Bagnis-Gabriele/Robotic-hand/photos/hands/High_five.jpg

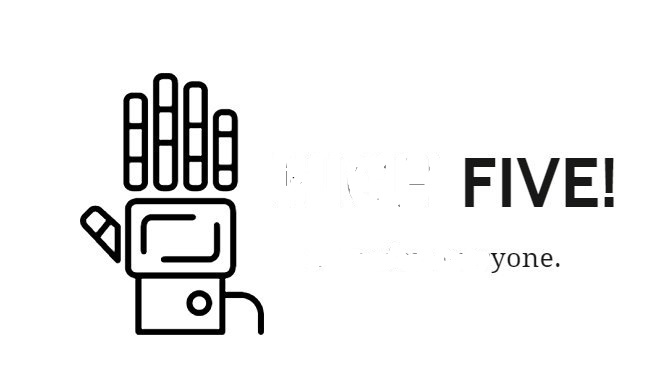
photos/hands/High_five.jpg
