Bagnis-Gabriele/Robotic-hand/photos/hands/mano_complited.jpg

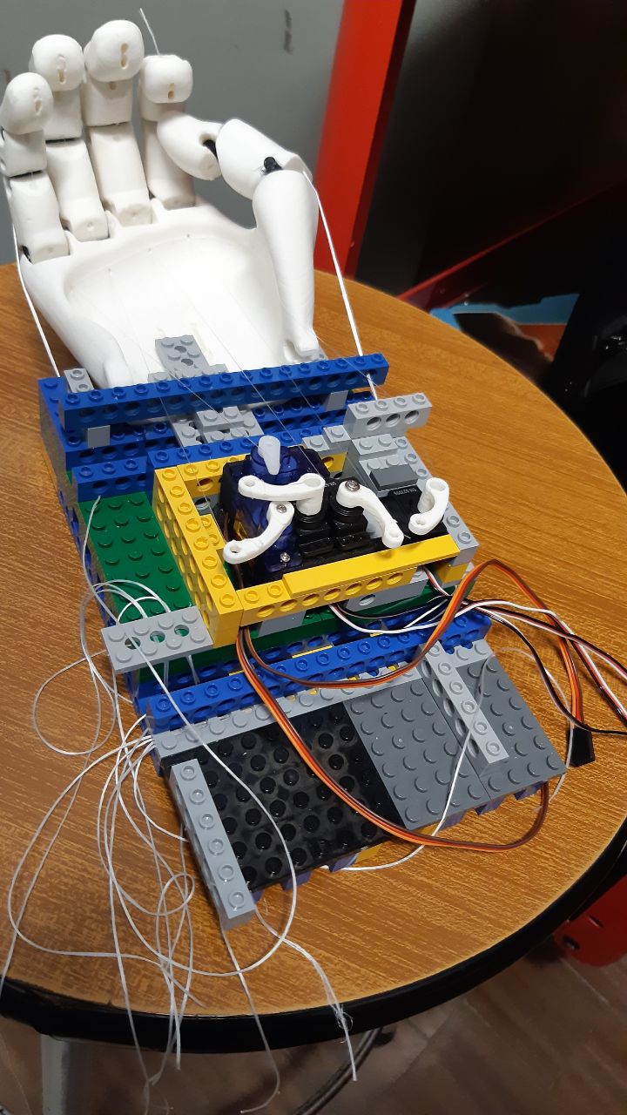
photos/hands/mano_complited.jpg
