Bagnis-Gabriele/Robotic-hand/photos/Insta/emotive.jpg

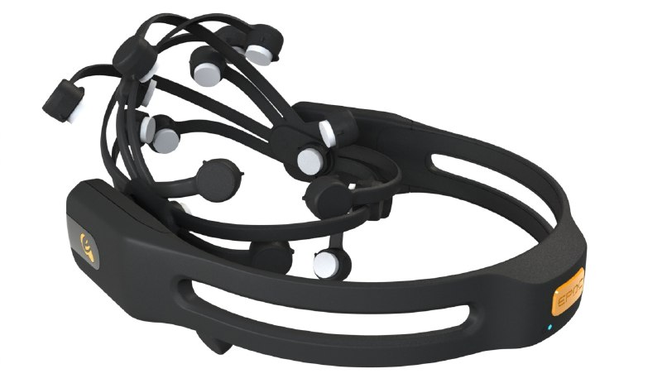
photos/Insta/emotive.jpg
