Bagnis-Gabriele/Robotic-hand/photos/Insta/leap.jpg

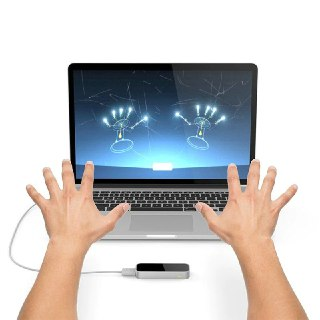
photos/Insta/leap.jpg
