Bagnis-Gabriele/Robotic-hand/photos/schemes/1.PNG

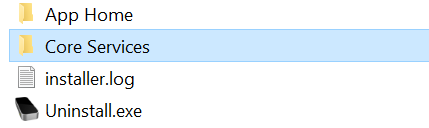
photos/schemes/1.PNG
