Bagnis-Gabriele/Robotic-hand/photos/schemes/2.PNG

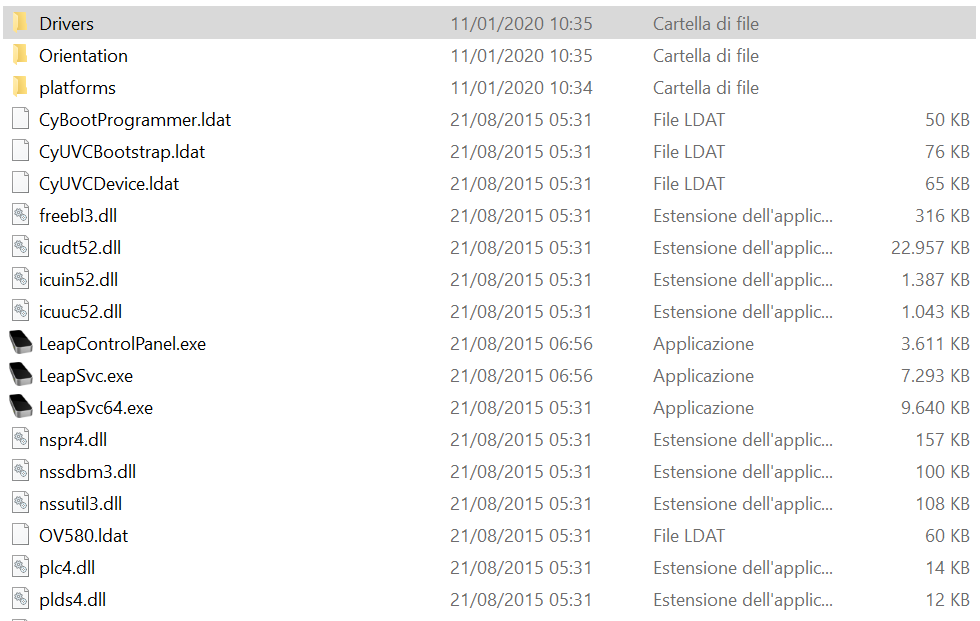
photos/schemes/2.PNG
