Bagnis-Gabriele/Robotic-hand/photos/schemes/3.PNG

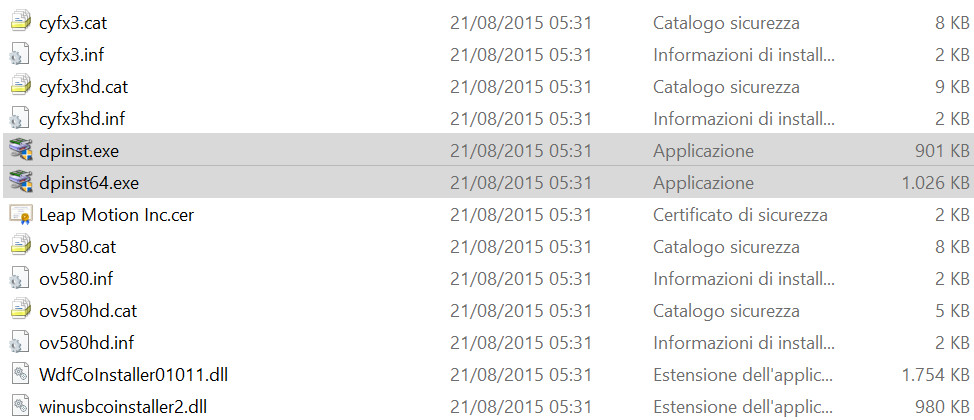
photos/schemes/3.PNG
