Bagnis-Gabriele/Robotic-hand/photos/schemes/broken_hand.jpg

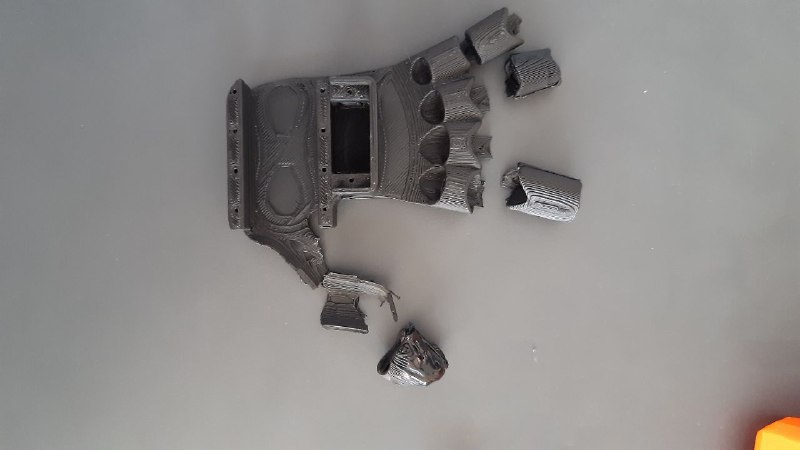
photos/schemes/broken_hand.jpg
