Bagnis-Gabriele/Robotic-hand/photos/schemes/brokenhand.jpg

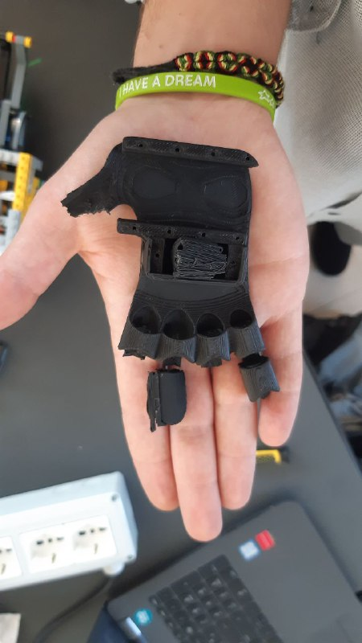
photos/schemes/brokenhand.jpg
