Bagnis-Gabriele/Robotic-hand/photos/schemes/manoo.jpg

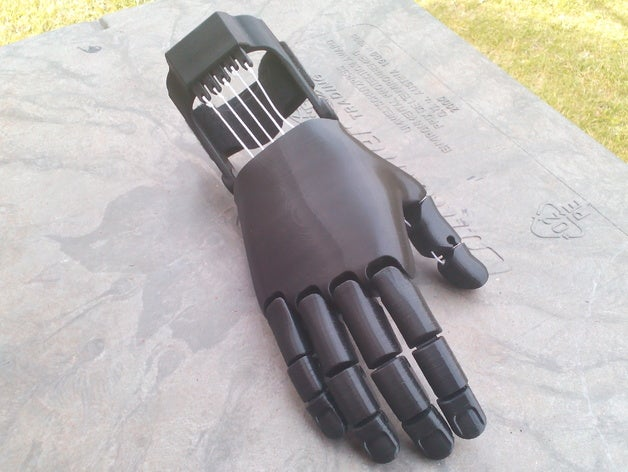
photos/schemes/manoo.jpg
