Bagnis-Gabriele/Robotic-hand/photos/Team/3dcreator.jpg

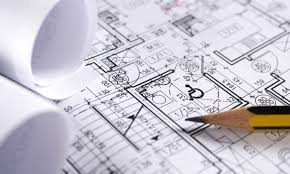
photos/Team/3dcreator.jpg
