Bagnis-Gabriele/Robotic-hand/photos/Team/Bruno.JPG

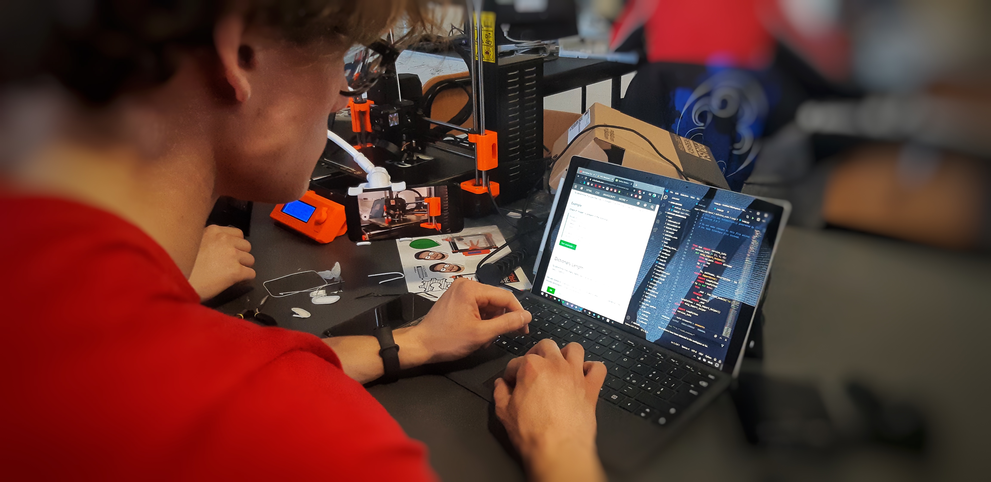
photos/Team/Bruno.JPG
