Bagnis-Gabriele/Robotic-hand/presentation/WBS.jpg

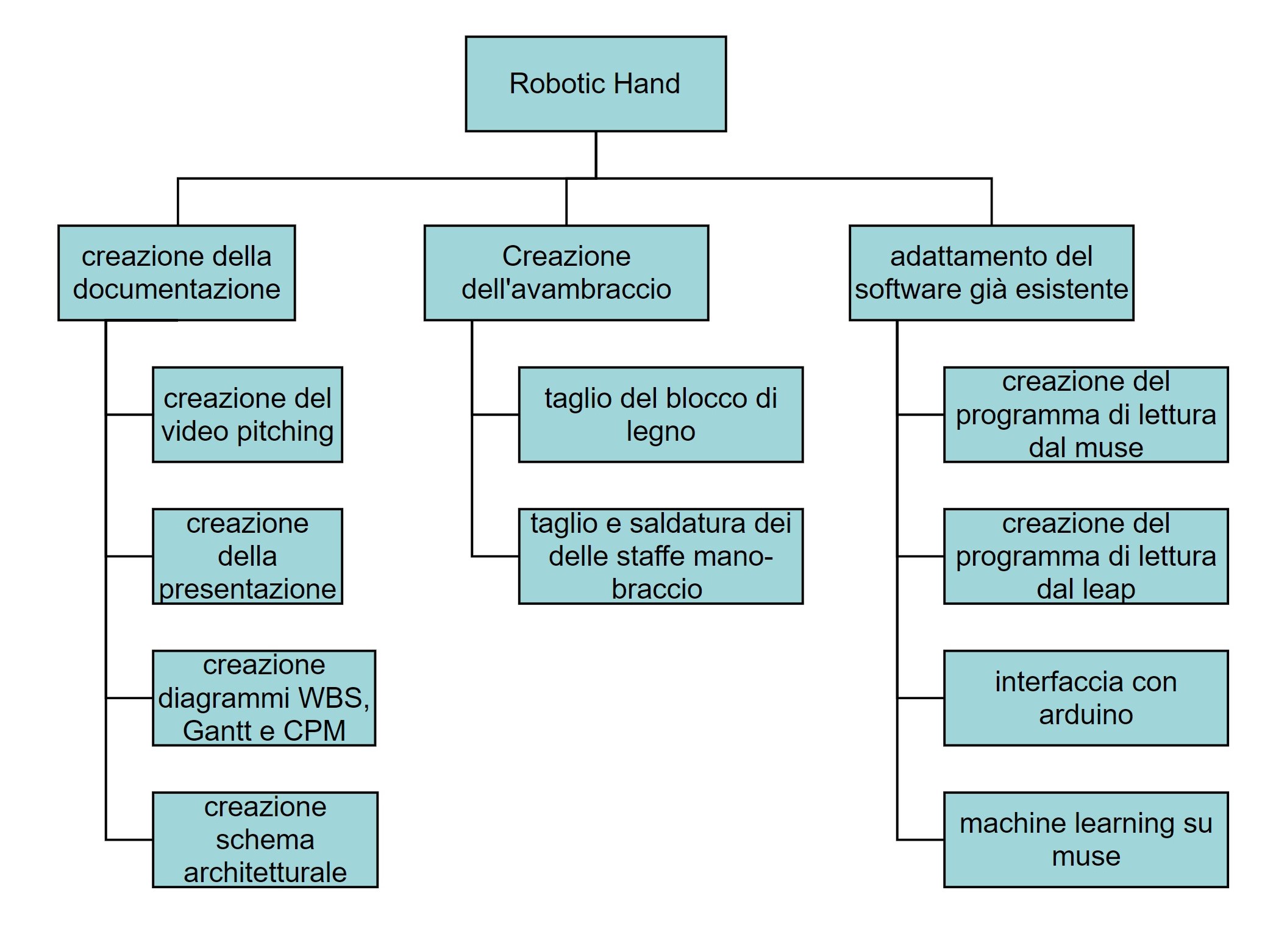
presentation/WBS.jpg
