Bagnis-Gabriele/Robotic-hand/3d model/ThermoForm_Palm_Mesh_Wide_Wrist.stl

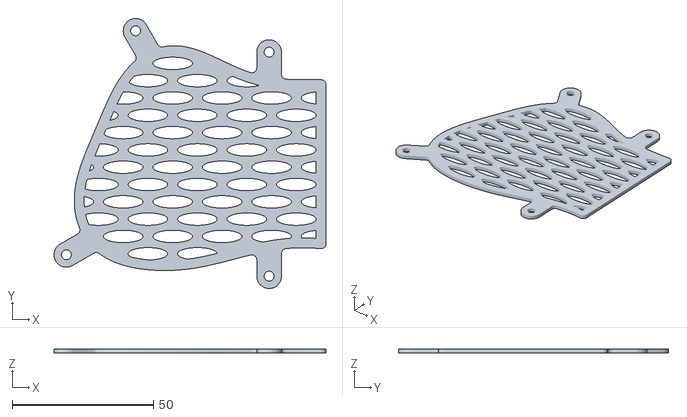
[picture p59: CAD file, 2020-01-13]
3d model/ThermoForm_Palm_Mesh_Wide_Wrist.stl
96.2 x 95.5 x 1.53
