Bagnis-Gabriele/Robotic-hand/3d model/RH_Hand_Body_-_Wider_Wrist.stl

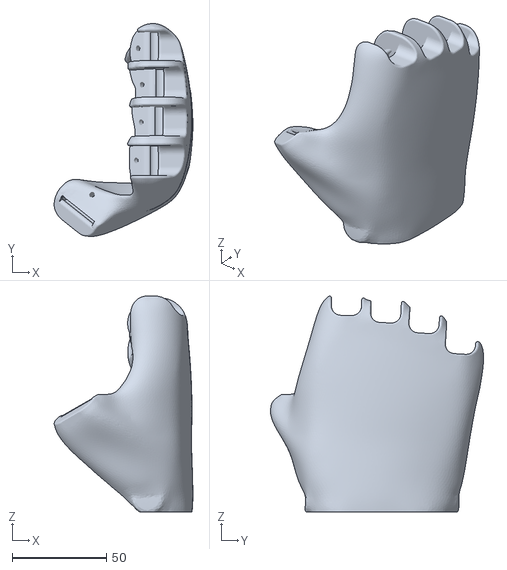
[picture p60: CAD file, 2020-01-13]
3d model/RH_Hand_Body_-_Wider_Wrist.stl
73.8 x 113.3 x 114.9
