Bagnis-Gabriele/Robotic-hand/3d model/Gauntlet_-_Short_Wider_Wrist.stl

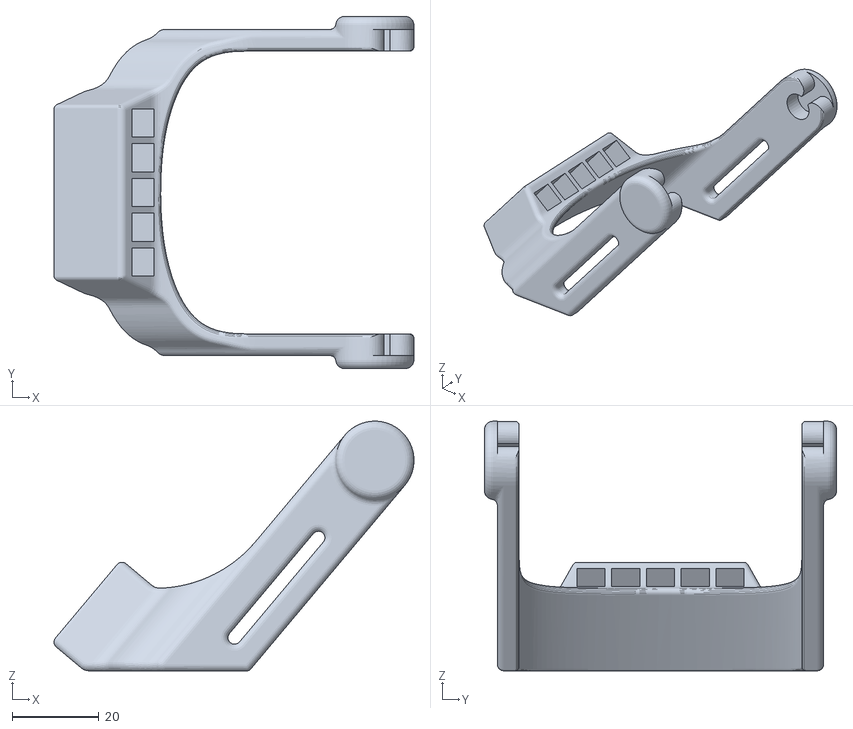
[picture p61: CAD file, 2020-01-13]
3d model/Gauntlet_-_Short_Wider_Wrist.stl
82.8 x 81.0 x 57.4
