Bagnis-Gabriele/Robotic-hand/3d model/Flexy-Hand_2_Gauntlet_-_Thermoform.stl

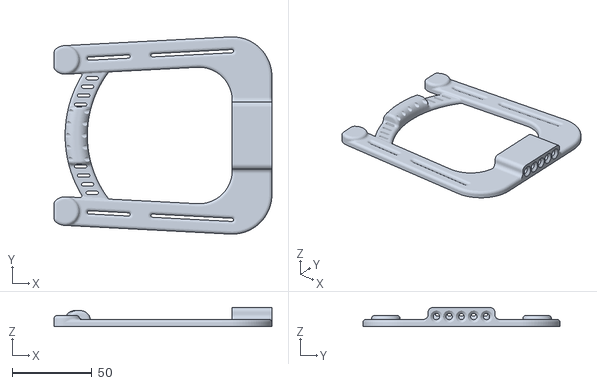
[picture p62: CAD file, 2020-01-13]
3d model/Flexy-Hand_2_Gauntlet_-_Thermoform.stl
137.0 x 123.9 x 12.0
