Bagnis-Gabriele/Robotic-hand/3d model/RH_Hand_Body_-_Wider_Wrist_-_Opposable_Thumb.stl

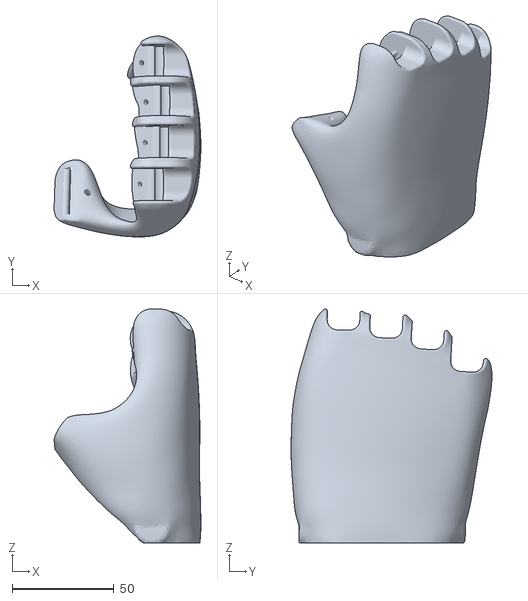
[picture p63: CAD file, 2020-01-13]
3d model/RH_Hand_Body_-_Wider_Wrist_-_Opposable_Thumb.stl
72.1 x 98.6 x 114.9
