Bagnis-Gabriele/Robotic-hand/3d model/ThermoForm_Palm_Mesh.stl

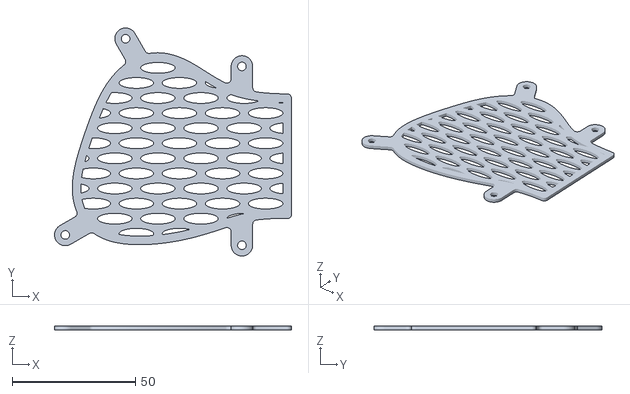
[picture p64: CAD file, 2020-01-13]
3d model/ThermoForm_Palm_Mesh.stl
96.3 x 92.6 x 1.53
