Bagnis-Gabriele/Robotic-hand/photos/schemes/Project_steps.jpg

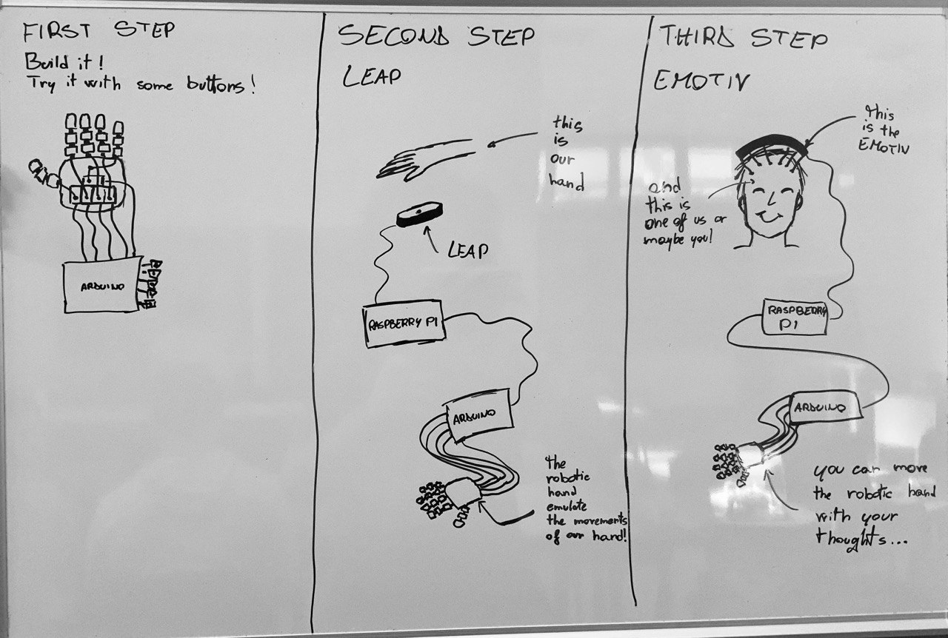
photos/schemes/Project_steps.jpg
